shanealexshibu1-crypto/Skippy/PCB/skippy 2.kicad_sch

## KiCad design PCB/skippy 2.kicad_sch (2026-07-09)

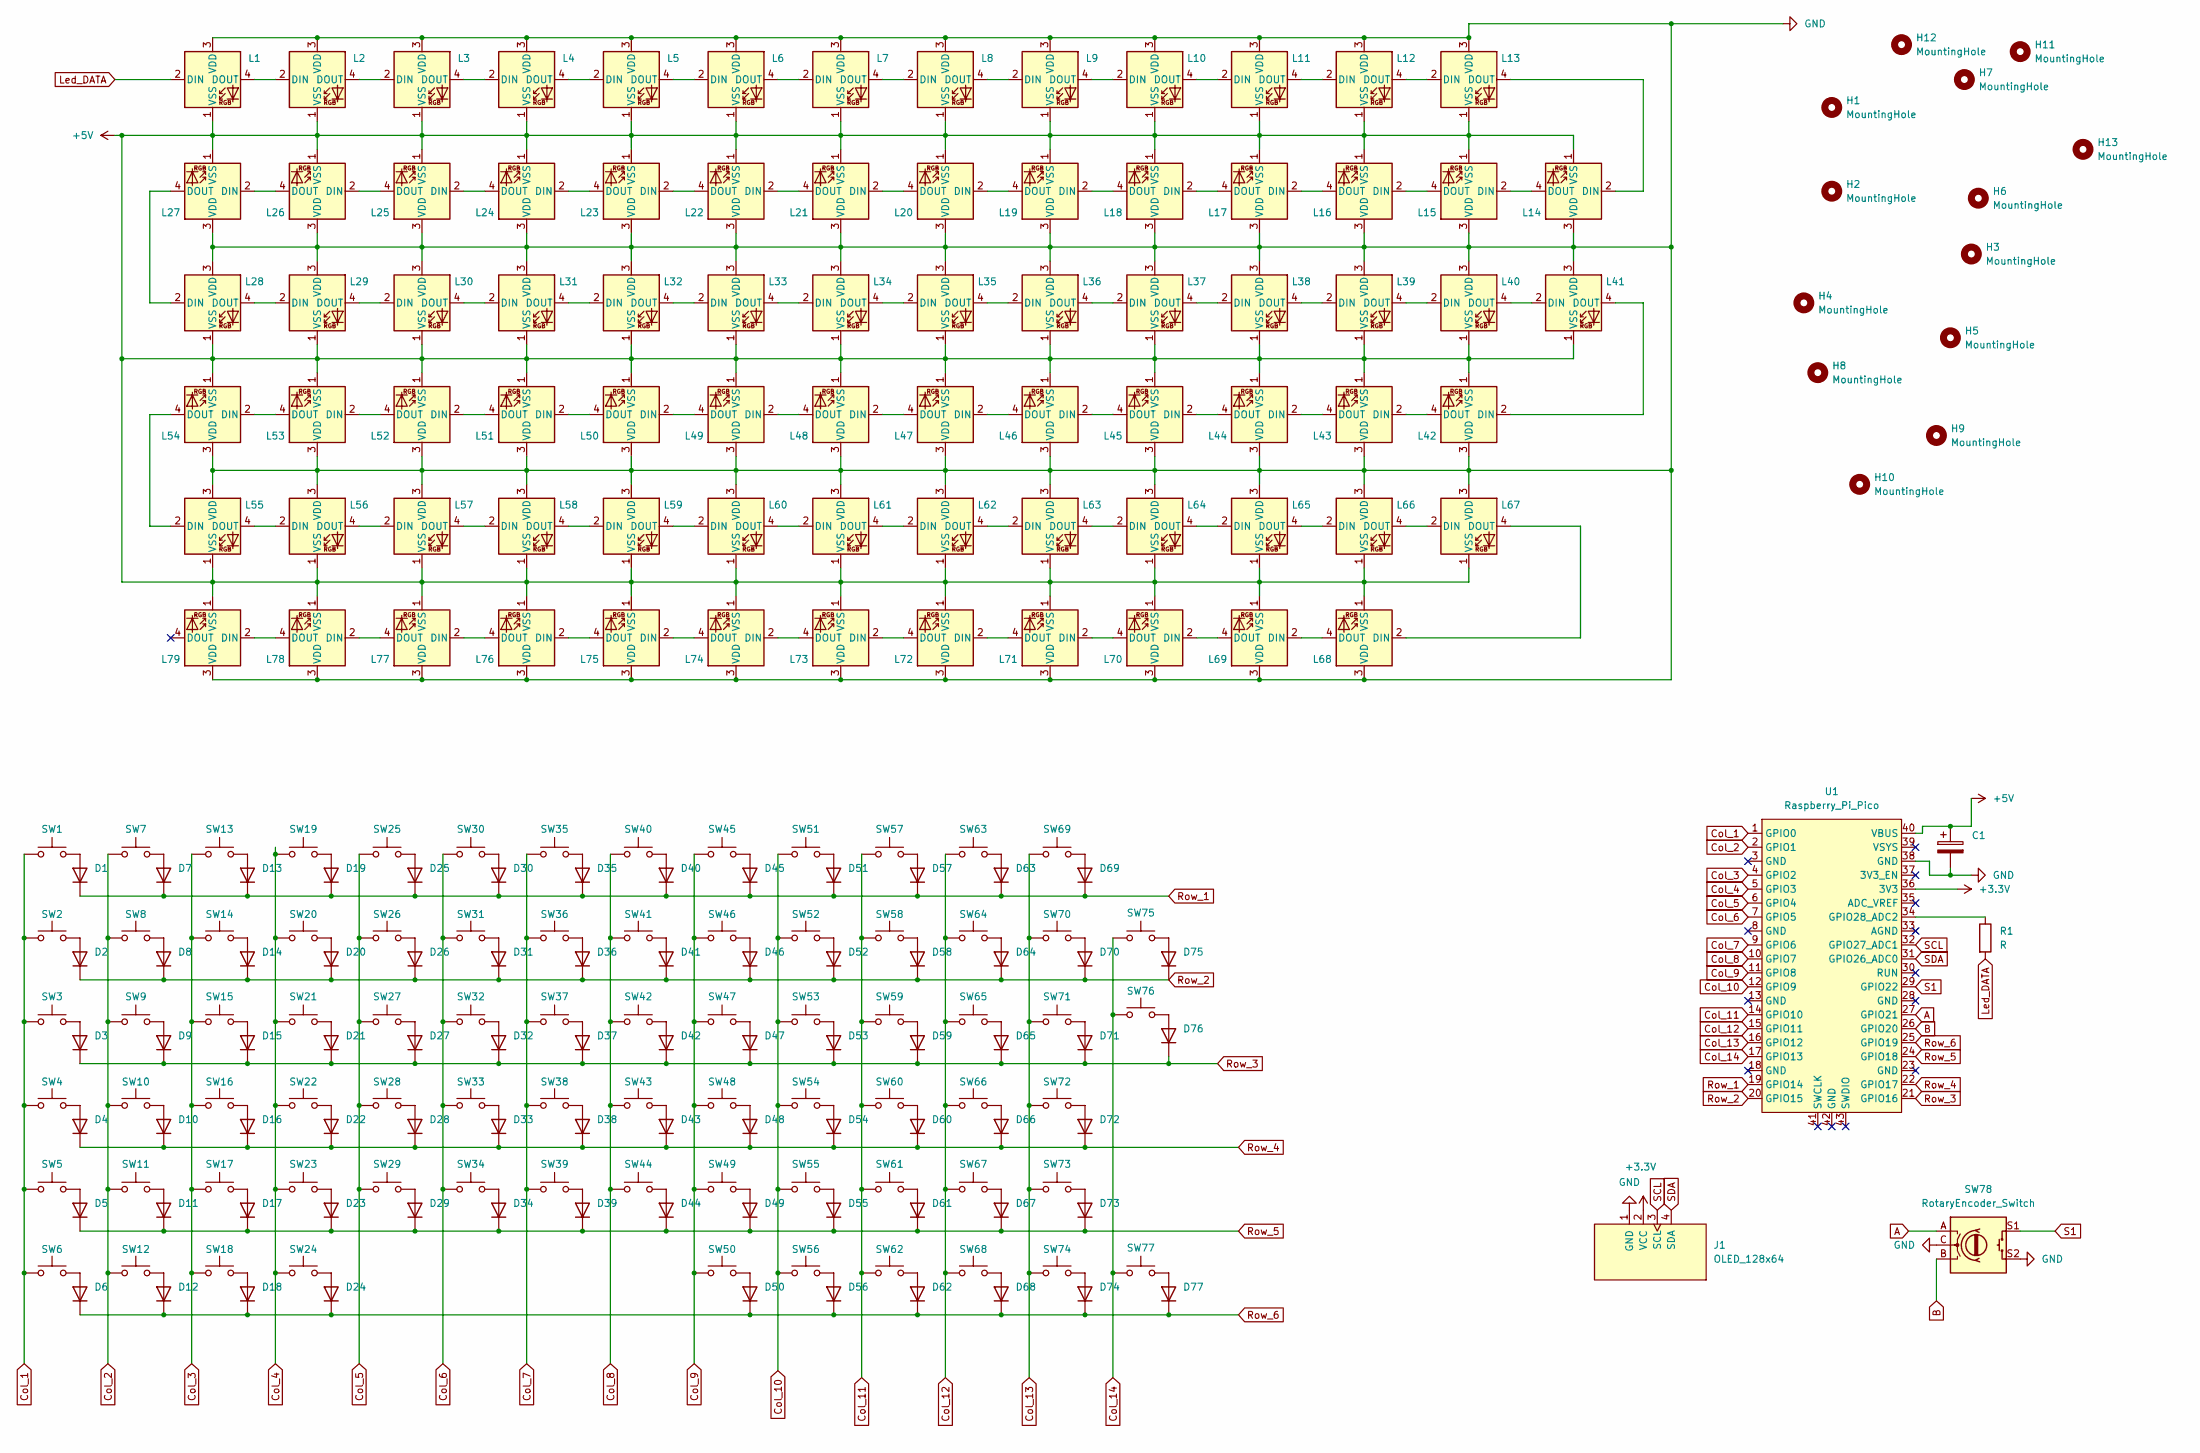
[picture p3: schematic skippy 2.kicad_sch]

Parts:
C1: C_Polarized; CP_Radial_D6.3mm_P2.50mm
D1, D2, D3, D4, D5, D6, D7, D8, D9, D10, D11, D12, D13, D14, D15, D16, D17, D18, D19, D20, D21, D22, D23, D24, D25, D26, D27, D28, D29, D30, D31, D32, D33, D34, D35, D36, D37, D38, D39, D40, D41, D42, D43, D44, D45, D46, D47, D48, D49, D50, D51, D52, D53, D54, D55, D56, D57, D58, D59, D60, D61, D62, D63, D64, D65, D66, D67, D68, D69, D70, D71, D72, D73, D74, D75, D76, D77: 1N914WT; Diode_DO-35
H1, H2, H3, H4, H5, H6, H7, H8, H9, H10, H11, H12, H13: MountingHole; Standoff_M2x4mm
J1: OLED_128x64
L1, L2, L3, L4, L5, L6, L7, L8, L9, L10, L11, L12, L13, L14, L15, L16, L17, L18, L19, L20, L21, L22, L23, L24, L25, L26, L27, L28, L29, L30, L31, L32, L33, L34, L35, L36, L37, L38, L39, L40, L41, L42, L43, L44, L45, L46, L47, L48, L49, L50, L51, L52, L53, L54, L55, L56, L57, L58, L59, L60, L61, L62, L63, L64, L65, L66, L67, L68, L69, L70, L71, L72, L73, L74, L75, L76, L77, L78, L79: SK6812MINI-E; LED_SK6812MINI-E_3.2x2.8mm_P1.5mm_ReverseMount_Shane
R1: R; R_Axial_DIN0207_L6.3mm_D2.5mm_P10.16mm_Horizontal
SW1, SW2, SW7, SW8, SW9, SW10, SW11, SW13, SW14, SW15, SW16, SW17, SW19, SW20, SW21, SW22, SW23, SW25, SW26, SW27, SW28, SW29, SW30, SW31, SW32, SW33, SW34, SW35, SW36, SW37, SW38, SW39, SW40, SW41, SW42, SW43, SW44, SW45, SW46, SW47, SW48, SW49, SW51, SW52, SW53, SW54, SW55, SW57, SW58, SW59, SW60, SW61, SW63, SW64, SW65, SW66, SW68, SW69, SW70, SW71, SW73, SW74, SW77: SW_Push; Hotswap_MX_1.00u
SW3, SW76: SW_Push; Hotswap_MX_1.50u
SW4: SW_Push; Hotswap_MX_1.75u
SW5, SW72: SW_Push; Hotswap_MX_2.25u
SW6, SW12, SW18, SW50, SW56, SW62: SW_Push; Hotswap_MX_1.25u
SW24: SW_Push; Hotswap_MX_6.25u
SW67: SW_Push; Hotswap_MX_2.75u
SW75: SW_Push; Hotswap_MX_2.00u
SW78: RotaryEncoder_Switch; RotaryEncoder_Alps_EC11E-Switch_Vertical_H20mm_MountingHoles
U1: Raspberry_Pi_Pico

Connections:
+3.3V: J1.2 (VCC), U1.36 (3V3)
+5V: C1.1, L1.1 (VSS), L2.1 (VSS), L3.1 (VSS), L4.1 (VSS), L5.1 (VSS), L6.1 (VSS), L7.1 (VSS), L8.1 (VSS), L9.1 (VSS), L10.1 (VSS), L11.1 (VSS), L12.1 (VSS), L13.1 (VSS), L14.1 (VSS), L15.1 (VSS), L16.1 (VSS), L17.1 (VSS), L18.1 (VSS), L19.1 (VSS), L20.1 (VSS), L21.1 (VSS), L22.1 (VSS), L23.1 (VSS), L24.1 (VSS), L25.1 (VSS), L26.1 (VSS), L27.1 (VSS), L28.1 (VSS), L29.1 (VSS), L30.1 (VSS), L31.1 (VSS), L32.1 (VSS), L33.1 (VSS), L34.1 (VSS), L35.1 (VSS), L36.1 (VSS), L37.1 (VSS), L38.1 (VSS), L39.1 (VSS), L40.1 (VSS), L41.1 (VSS), L42.1 (VSS), L43.1 (VSS), L44.1 (VSS), L45.1 (VSS), L46.1 (VSS), L47.1 (VSS), L48.1 (VSS), L49.1 (VSS), L50.1 (VSS), L51.1 (VSS), L52.1 (VSS), L53.1 (VSS), L54.1 (VSS), L55.1 (VSS), L56.1 (VSS), L57.1 (VSS), L58.1 (VSS), L59.1 (VSS), L60.1 (VSS), L61.1 (VSS), L62.1 (VSS), L63.1 (VSS), L64.1 (VSS), L65.1 (VSS), L66.1 (VSS), L67.1 (VSS), L68.1 (VSS), L69.1 (VSS), L70.1 (VSS), L71.1 (VSS), L72.1 (VSS), L73.1 (VSS), L74.1 (VSS), L75.1 (VSS), L76.1 (VSS), L77.1 (VSS), L78.1 (VSS), L79.1 (VSS), U1.40 (VBUS)
A: SW78.A, U1.27 (GPIO21)
B: SW78.B, U1.26 (GPIO20)
Col_1: SW1.1, SW2.1, SW3.1, SW4.1, SW5.1, SW6.1, U1.1 (GPIO0)
Col_2: SW7.1, SW8.1, SW9.1, SW10.1, SW11.1, SW12.1, U1.2 (GPIO1)
Col_3: SW13.1, SW14.1, SW15.1, SW16.1, SW17.1, SW18.1, U1.4 (GPIO2)
Col_4: SW19.1, SW20.1, SW21.1, SW22.1, SW23.1, SW24.1, U1.5 (GPIO3)
Col_5: SW25.1, SW26.1, SW27.1, SW28.1, SW29.1, U1.6 (GPIO4)
Col_6: SW30.1, SW31.1, SW32.1, SW33.1, SW34.1, U1.7 (GPIO5)
Col_7: SW35.1, SW36.1, SW37.1, SW38.1, SW39.1, U1.9 (GPIO6)
Col_8: SW40.1, SW41.1, SW42.1, SW43.1, SW44.1, U1.10 (GPIO7)
Col_9: SW45.1, SW46.1, SW47.1, SW48.1, SW49.1, SW50.1, U1.11 (GPIO8)
Col_10: SW51.1, SW52.1, SW53.1, SW54.1, SW55.1, SW56.1, U1.12 (GPIO9)
Col_11: SW57.1, SW58.1, SW59.1, SW60.1, SW61.1, SW62.1, U1.14 (GPIO10)
Col_12: SW63.1, SW64.1, SW65.1, SW66.1, SW67.1, SW68.1, U1.15 (GPIO11)
Col_13: SW69.1, SW70.1, SW71.1, SW72.1, SW73.1, SW74.1, U1.16 (GPIO12)
Col_14: SW75.1, SW76.1, SW77.1, U1.17 (GPIO13)
GND: C1.2, J1.1 (GND), L1.3 (VDD), L2.3 (VDD), L3.3 (VDD), L4.3 (VDD), L5.3 (VDD), L6.3 (VDD), L7.3 (VDD), L8.3 (VDD), L9.3 (VDD), L10.3 (VDD), L11.3 (VDD), L12.3 (VDD), L13.3 (VDD), L14.3 (VDD), L15.3 (VDD), L16.3 (VDD), L17.3 (VDD), L18.3 (VDD), L19.3 (VDD), L20.3 (VDD), L21.3 (VDD), L22.3 (VDD), L23.3 (VDD), L24.3 (VDD), L25.3 (VDD), L26.3 (VDD), L27.3 (VDD), L28.3 (VDD), L29.3 (VDD), L30.3 (VDD), L31.3 (VDD), L32.3 (VDD), L33.3 (VDD), L34.3 (VDD), L35.3 (VDD), L36.3 (VDD), L37.3 (VDD), L38.3 (VDD), L39.3 (VDD), L40.3 (VDD), L41.3 (VDD), L42.3 (VDD), L43.3 (VDD), L44.3 (VDD), L45.3 (VDD), L46.3 (VDD), L47.3 (VDD), L48.3 (VDD), L49.3 (VDD), L50.3 (VDD), L51.3 (VDD), L52.3 (VDD), L53.3 (VDD), L54.3 (VDD), L55.3 (VDD), L56.3 (VDD), L57.3 (VDD), L58.3 (VDD), L59.3 (VDD), L60.3 (VDD), L61.3 (VDD), L62.3 (VDD), L63.3 (VDD), L64.3 (VDD), L65.3 (VDD), L66.3 (VDD), L67.3 (VDD), L68.3 (VDD), L69.3 (VDD), L70.3 (VDD), L71.3 (VDD), L72.3 (VDD), L73.3 (VDD), L74.3 (VDD), L75.3 (VDD), L76.3 (VDD), L77.3 (VDD), L78.3 (VDD), L79.3 (VDD), SW78.C, SW78.S2, U1.38 (GND)
Led_DATA: L1.2 (DIN), R1.2
unnamed: D1.2 (A), SW1.2
unnamed: D2.2 (A), SW2.2
unnamed: D3.2 (A), SW3.2
unnamed: D4.2 (A), SW4.2
unnamed: D5.2 (A), SW5.2
unnamed: D6.2 (A), SW6.2
unnamed: D7.2 (A), SW7.2
unnamed: D8.2 (A), SW8.2
unnamed: D9.2 (A), SW9.2
unnamed: D10.2 (A), SW10.2
unnamed: D11.2 (A), SW11.2
unnamed: D12.2 (A), SW12.2
unnamed: D13.2 (A), SW13.2
unnamed: D14.2 (A), SW14.2
unnamed: D15.2 (A), SW15.2
unnamed: D16.2 (A), SW16.2
unnamed: D17.2 (A), SW17.2
unnamed: D18.2 (A), SW18.2
unnamed: D19.2 (A), SW19.2
unnamed: D20.2 (A), SW20.2
unnamed: D21.2 (A), SW21.2
unnamed: D22.2 (A), SW22.2
unnamed: D23.2 (A), SW23.2
unnamed: D24.2 (A), SW24.2
unnamed: D25.2 (A), SW25.2
unnamed: D26.2 (A), SW26.2
unnamed: D27.2 (A), SW27.2
unnamed: D28.2 (A), SW28.2
unnamed: D29.2 (A), SW29.2
unnamed: D30.2 (A), SW30.2
unnamed: D31.2 (A), SW31.2
unnamed: D32.2 (A), SW32.2
unnamed: D33.2 (A), SW33.2
unnamed: D34.2 (A), SW34.2
unnamed: D35.2 (A), SW35.2
unnamed: D36.2 (A), SW36.2
unnamed: D37.2 (A), SW37.2
unnamed: D38.2 (A), SW38.2
unnamed: D39.2 (A), SW39.2
unnamed: D40.2 (A), SW40.2
unnamed: D41.2 (A), SW41.2
unnamed: D42.2 (A), SW42.2
unnamed: D43.2 (A), SW43.2
unnamed: D44.2 (A), SW44.2
unnamed: D45.2 (A), SW45.2
unnamed: D46.2 (A), SW46.2
unnamed: D47.2 (A), SW47.2
unnamed: D48.2 (A), SW48.2
unnamed: D49.2 (A), SW49.2
unnamed: D50.2 (A), SW50.2
unnamed: D51.2 (A), SW51.2
unnamed: D52.2 (A), SW52.2
unnamed: D53.2 (A), SW53.2
unnamed: D54.2 (A), SW54.2
unnamed: D55.2 (A), SW55.2
unnamed: D56.2 (A), SW56.2
unnamed: D57.2 (A), SW57.2
unnamed: D58.2 (A), SW58.2
unnamed: D59.2 (A), SW59.2
unnamed: D60.2 (A), SW60.2
unnamed: D61.2 (A), SW61.2
unnamed: D62.2 (A), SW62.2
unnamed: D63.2 (A), SW63.2
unnamed: D64.2 (A), SW64.2
unnamed: D65.2 (A), SW65.2
unnamed: D66.2 (A), SW66.2
unnamed: D67.2 (A), SW67.2
unnamed: D68.2 (A), SW68.2
unnamed: D69.2 (A), SW69.2
unnamed: D70.2 (A), SW70.2
unnamed: D71.2 (A), SW71.2
unnamed: D72.2 (A), SW72.2
unnamed: D73.2 (A), SW73.2
unnamed: D74.2 (A), SW74.2
unnamed: D75.2 (A), SW75.2
unnamed: D76.2 (A), SW76.2
unnamed: D77.2 (A), SW77.2
unnamed: L1.4 (DOUT), L2.2 (DIN)
unnamed: L2.4 (DOUT), L3.2 (DIN)
unnamed: L3.4 (DOUT), L4.2 (DIN)
unnamed: L4.4 (DOUT), L5.2 (DIN)
unnamed: L5.4 (DOUT), L6.2 (DIN)
unnamed: L6.4 (DOUT), L7.2 (DIN)
unnamed: L7.4 (DOUT), L8.2 (DIN)
unnamed: L8.4 (DOUT), L9.2 (DIN)
unnamed: L9.4 (DOUT), L10.2 (DIN)
unnamed: L10.4 (DOUT), L11.2 (DIN)
unnamed: L11.4 (DOUT), L12.2 (DIN)
unnamed: L12.4 (DOUT), L13.2 (DIN)
unnamed: L13.4 (DOUT), L14.2 (DIN)
unnamed: L14.4 (DOUT), L15.2 (DIN)
unnamed: L15.4 (DOUT), L16.2 (DIN)
unnamed: L16.4 (DOUT), L17.2 (DIN)
unnamed: L17.4 (DOUT), L18.2 (DIN)
unnamed: L18.4 (DOUT), L19.2 (DIN)
unnamed: L19.4 (DOUT), L20.2 (DIN)
unnamed: L20.4 (DOUT), L21.2 (DIN)
unnamed: L21.4 (DOUT), L22.2 (DIN)
unnamed: L22.4 (DOUT), L23.2 (DIN)
unnamed: L23.4 (DOUT), L24.2 (DIN)
unnamed: L24.4 (DOUT), L25.2 (DIN)
unnamed: L25.4 (DOUT), L26.2 (DIN)
unnamed: L26.4 (DOUT), L27.2 (DIN)
unnamed: L27.4 (DOUT), L28.2 (DIN)
unnamed: L28.4 (DOUT), L29.2 (DIN)
unnamed: L29.4 (DOUT), L30.2 (DIN)
unnamed: L30.4 (DOUT), L31.2 (DIN)
unnamed: L31.4 (DOUT), L32.2 (DIN)
unnamed: L32.4 (DOUT), L33.2 (DIN)
unnamed: L33.4 (DOUT), L34.2 (DIN)
unnamed: L34.4 (DOUT), L35.2 (DIN)
unnamed: L35.4 (DOUT), L36.2 (DIN)
unnamed: L36.4 (DOUT), L37.2 (DIN)
unnamed: L37.4 (DOUT), L38.2 (DIN)
unnamed: L38.4 (DOUT), L39.2 (DIN)
unnamed: L39.4 (DOUT), L40.2 (DIN)
unnamed: L40.4 (DOUT), L41.2 (DIN)
unnamed: L41.4 (DOUT), L42.2 (DIN)
unnamed: L42.4 (DOUT), L43.2 (DIN)
unnamed: L43.4 (DOUT), L44.2 (DIN)
unnamed: L44.4 (DOUT), L45.2 (DIN)
unnamed: L45.4 (DOUT), L46.2 (DIN)
unnamed: L46.4 (DOUT), L47.2 (DIN)
unnamed: L47.4 (DOUT), L48.2 (DIN)
unnamed: L48.4 (DOUT), L49.2 (DIN)
unnamed: L49.4 (DOUT), L50.2 (DIN)
unnamed: L50.4 (DOUT), L51.2 (DIN)
unnamed: L51.4 (DOUT), L52.2 (DIN)
unnamed: L52.4 (DOUT), L53.2 (DIN)
unnamed: L53.4 (DOUT), L54.2 (DIN)
unnamed: L54.4 (DOUT), L55.2 (DIN)
unnamed: L55.4 (DOUT), L56.2 (DIN)
unnamed: L56.4 (DOUT), L57.2 (DIN)
unnamed: L57.4 (DOUT), L58.2 (DIN)
unnamed: L58.4 (DOUT), L59.2 (DIN)
unnamed: L59.4 (DOUT), L60.2 (DIN)
unnamed: L60.4 (DOUT), L61.2 (DIN)
unnamed: L61.4 (DOUT), L62.2 (DIN)
unnamed: L62.4 (DOUT), L63.2 (DIN)
unnamed: L63.4 (DOUT), L64.2 (DIN)
unnamed: L64.4 (DOUT), L65.2 (DIN)
unnamed: L65.4 (DOUT), L66.2 (DIN)
unnamed: L66.4 (DOUT), L67.2 (DIN)
unnamed: L67.4 (DOUT), L68.2 (DIN)
unnamed: L68.4 (DOUT), L69.2 (DIN)
unnamed: L69.4 (DOUT), L70.2 (DIN)
unnamed: L70.4 (DOUT), L71.2 (DIN)
unnamed: L71.4 (DOUT), L72.2 (DIN)
unnamed: L72.4 (DOUT), L73.2 (DIN)
unnamed: L73.4 (DOUT), L74.2 (DIN)
unnamed: L74.4 (DOUT), L75.2 (DIN)
unnamed: L75.4 (DOUT), L76.2 (DIN)
unnamed: L76.4 (DOUT), L77.2 (DIN)
unnamed: L77.4 (DOUT), L78.2 (DIN)
unnamed: L78.4 (DOUT), L79.2 (DIN)
unnamed: R1.1, U1.34 (GPIO28_ADC2)
Row_1: D1.1 (K), D7.1 (K), D13.1 (K), D19.1 (K), D25.1 (K), D30.1 (K), D35.1 (K), D40.1 (K), D45.1 (K), D51.1 (K), D57.1 (K), D63.1 (K), D69.1 (K), U1.19 (GPIO14)
Row_2: D2.1 (K), D8.1 (K), D14.1 (K), D20.1 (K), D26.1 (K), D31.1 (K), D36.1 (K), D41.1 (K), D46.1 (K), D52.1 (K), D58.1 (K), D64.1 (K), D70.1 (K), D75.1 (K), U1.20 (GPIO15)
Row_3: D3.1 (K), D9.1 (K), D15.1 (K), D21.1 (K), D27.1 (K), D32.1 (K), D37.1 (K), D42.1 (K), D47.1 (K), D53.1 (K), D59.1 (K), D65.1 (K), D71.1 (K), D76.1 (K), U1.21 (GPIO16)
Row_4: D4.1 (K), D10.1 (K), D16.1 (K), D22.1 (K), D28.1 (K), D33.1 (K), D38.1 (K), D43.1 (K), D48.1 (K), D54.1 (K), D60.1 (K), D66.1 (K), D72.1 (K), U1.22 (GPIO17)
Row_5: D5.1 (K), D11.1 (K), D17.1 (K), D23.1 (K), D29.1 (K), D34.1 (K), D39.1 (K), D44.1 (K), D49.1 (K), D55.1 (K), D61.1 (K), D67.1 (K), D73.1 (K), U1.24 (GPIO18)
Row_6: D6.1 (K), D12.1 (K), D18.1 (K), D24.1 (K), D50.1 (K), D56.1 (K), D62.1 (K), D68.1 (K), D74.1 (K), D77.1 (K), U1.25 (GPIO19)
S1: SW78.S1, U1.29 (GPIO22)
SCL: J1.3 (SCL), U1.32 (GPIO27_ADC1)
SDA: J1.4 (SDA), U1.31 (GPIO26_ADC0)
